prakashlab/handyfuge/designs/v0.1.4/1.5 mL tubes/0.125 in/Rotor Cap 2.dxf

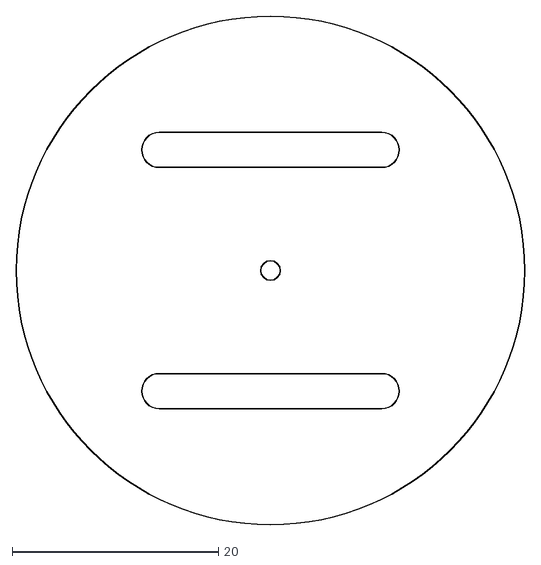
[picture p18: CAD file, 2020-07-03, an earlier design]
designs/v0.1.4/1.5 mL tubes/0.125 in/Rotor Cap 2.dxf
49.4 x 49.4
