prakashlab/handyfuge/designs/v0.2.2/1.5 mL tubes, rotor guard, small rotor/2 mm/Rotor Cap 1.dxf

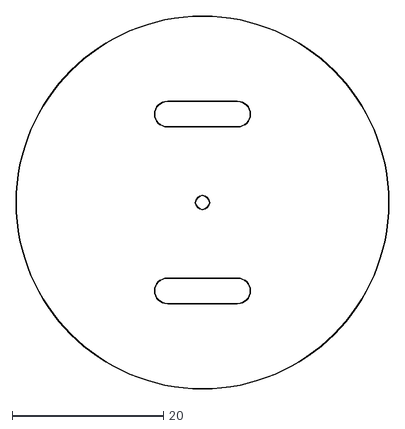
[picture p19: CAD file, 2020-07-03, an earlier design]
designs/v0.2.2/1.5 mL tubes, rotor guard, small rotor/2 mm/Rotor Cap 1.dxf
49.4 x 49.4
