prakashlab/handyfuge/designs/v0.2.2/1.5 mL tubes, rotor guard, small rotor/2 mm/Rotor Holder.dxf

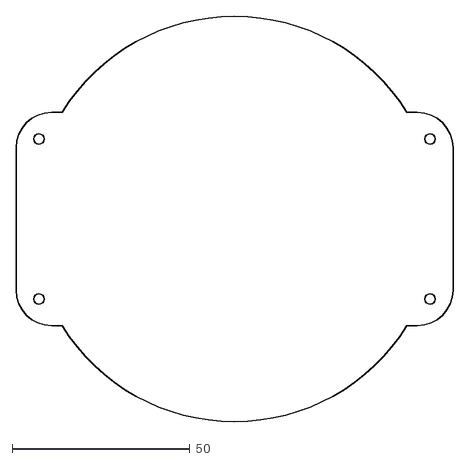
[picture p20: CAD file, 2020-07-03, an earlier design]
designs/v0.2.2/1.5 mL tubes, rotor guard, small rotor/2 mm/Rotor Holder.dxf
122.9 x 114.0
