prakashlab/handyfuge/designs/v0.2.2/1.5 mL tubes, rotor guard, small rotor/2 mm/Upper Axle Footprint.dxf

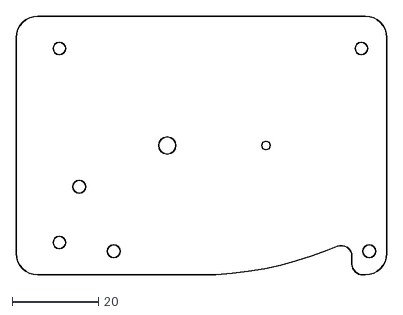
[picture p21: CAD file, 2020-07-03, an earlier design]
designs/v0.2.2/1.5 mL tubes, rotor guard, small rotor/2 mm/Upper Axle Footprint.dxf
85.9 x 60.0
